lakiluk86/Tank/doc/pics/IMG_20250106_113242.jpg

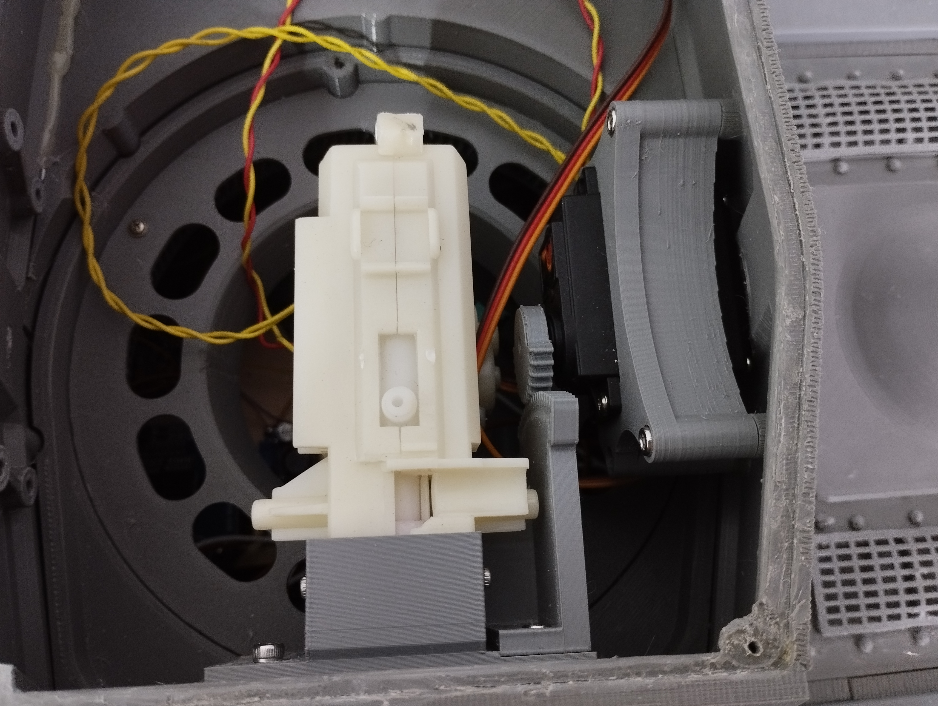
doc/pics/IMG_20250106_113242.jpg
