lakiluk86/Tank/doc/pics/IMG_20250113_225445.jpg

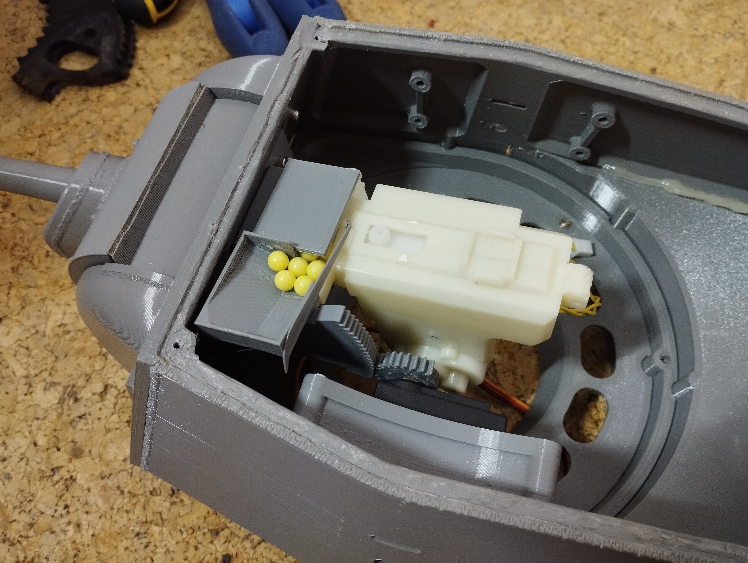
doc/pics/IMG_20250113_225445.jpg
