lakiluk86/Tank/doc/pics/IMG_20250113_225511.jpg

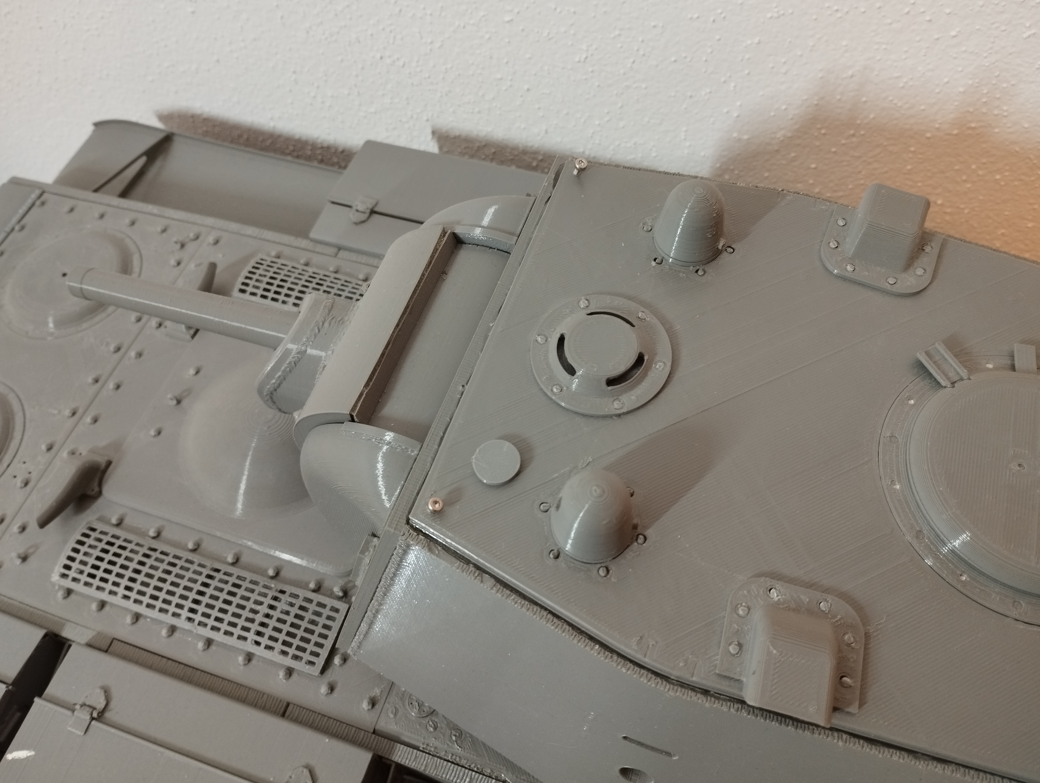
doc/pics/IMG_20250113_225511.jpg
